ericcarmi/3WDrobot/CAD files/lens/lensconnect.stl

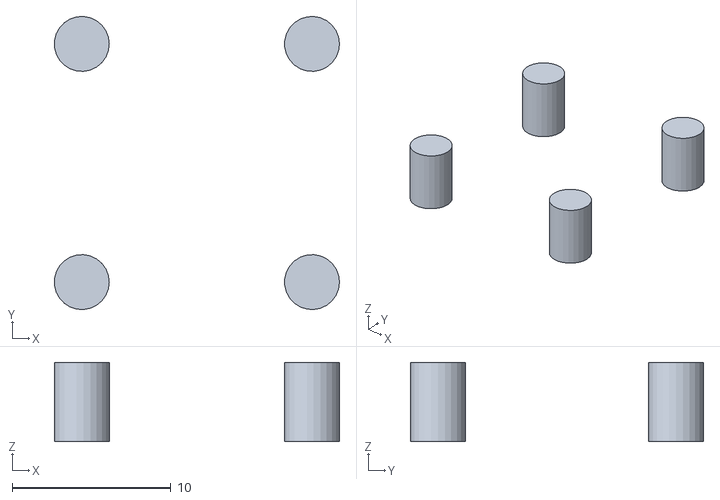
[picture p16: CAD file, 2020-05-03]
CAD files/lens/lensconnect.stl
18.0 x 18.5 x 5.00
