ericcarmi/3WDrobot/CAD files/hBridgeHolder.stl

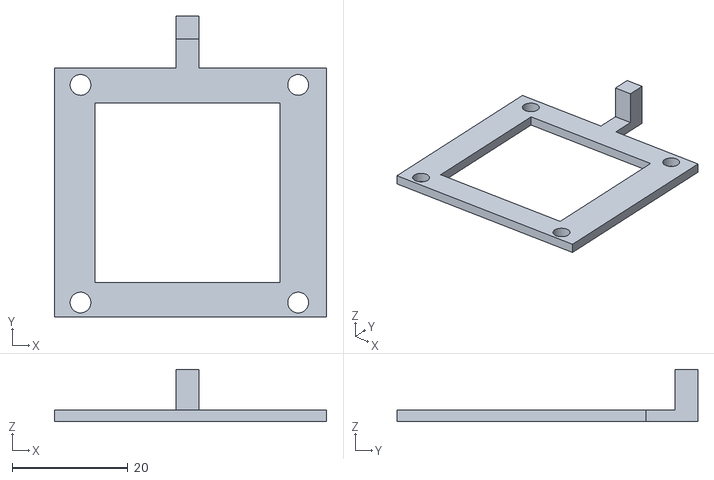
[picture p17: CAD file, 2020-05-03]
CAD files/hBridgeHolder.stl
47.0 x 52.0 x 9.00
