ericcarmi/3WDrobot/CAD files/cammountUnderBase.stl

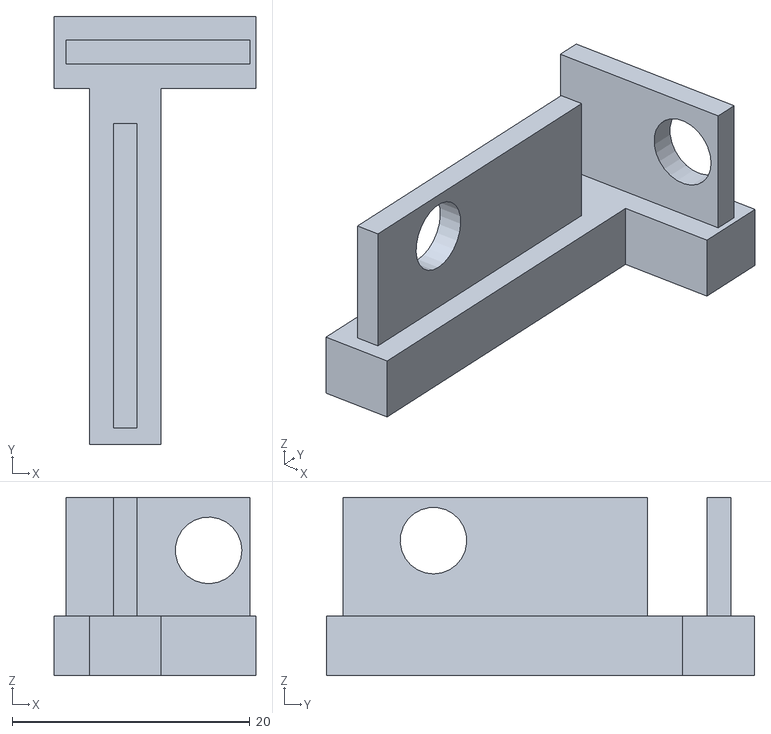
[picture p18: CAD file, 2020-05-03]
CAD files/cammountUnderBase.stl
17.0 x 36.0 x 15.0
