ericcarmi/3WDrobot/CAD files/cameraMount3.stl

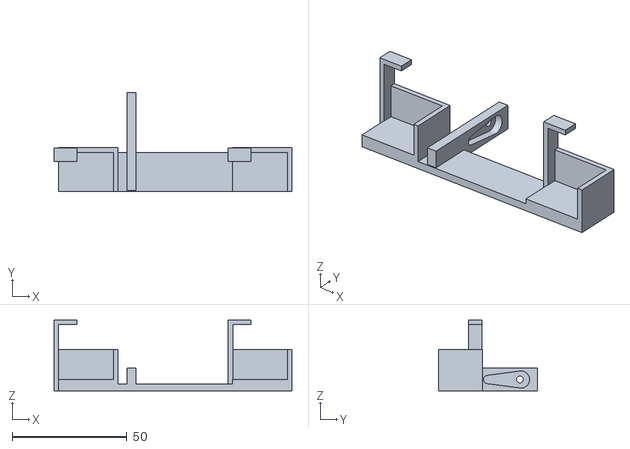
[picture p19: CAD file, 2020-05-03]
CAD files/cameraMount3.stl
103.9 x 43.0 x 31.0
