ericcarmi/3WDrobot/CAD files/robotmount.stl

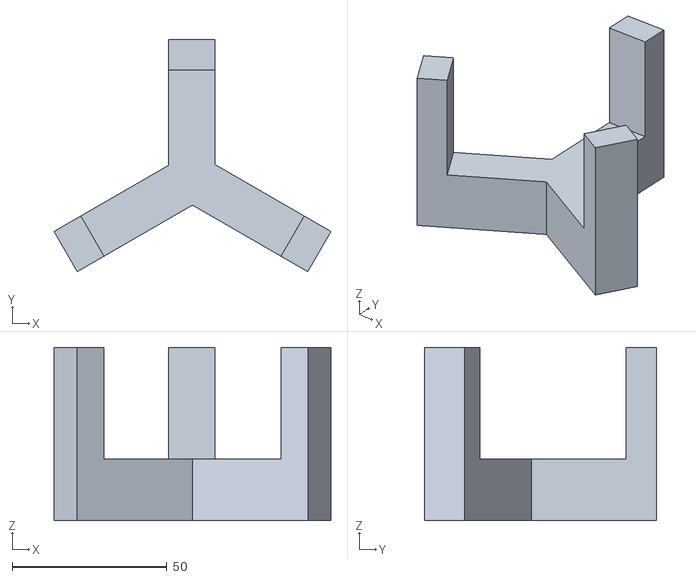
[picture p20: CAD file, 2020-05-03]
CAD files/robotmount.stl
89.5 x 75.1 x 56.0
