ericcarmi/3WDrobot/CAD files/stpprMicTop.stl

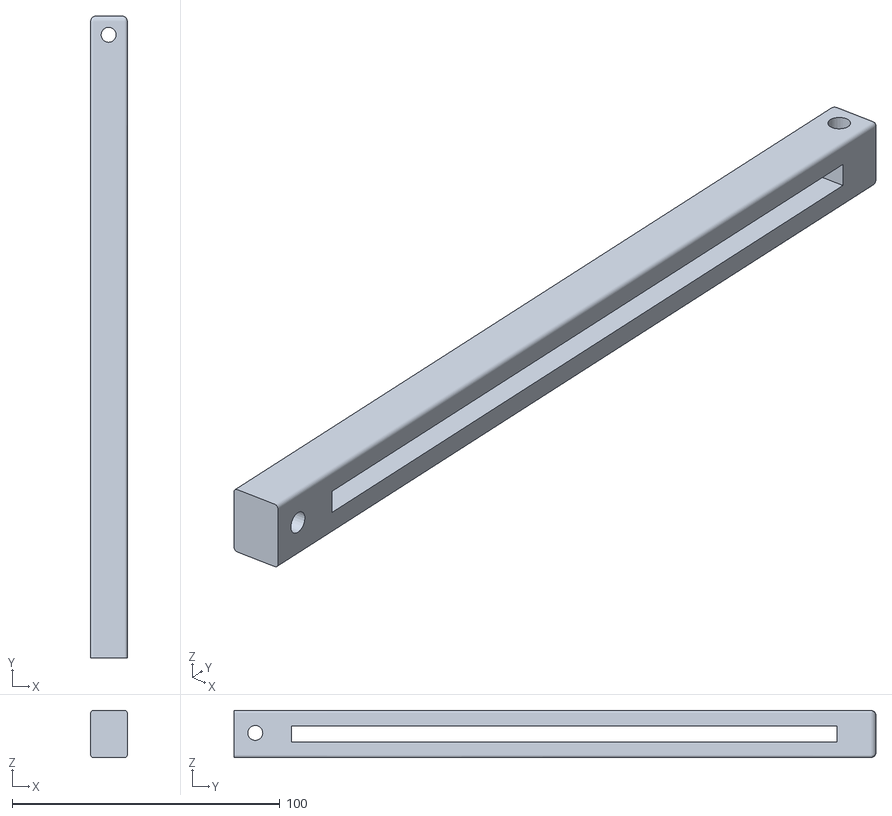
[picture p21: CAD file, 2020-05-03]
CAD files/stpprMicTop.stl
13.7 x 240.0 x 17.7
