ericcarmi/3WDrobot/CAD files/cammountBase.stl

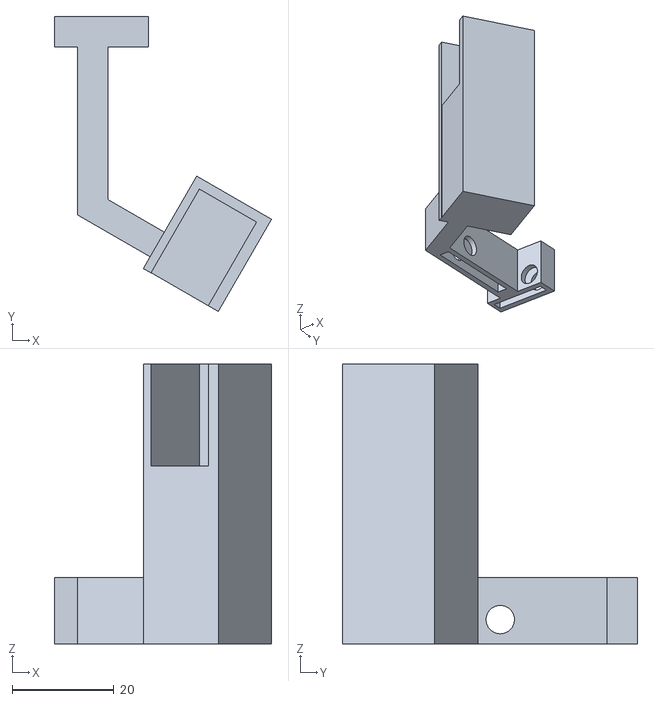
[picture p22: CAD file, 2020-05-03]
CAD files/cammountBase.stl
42.7 x 58.0 x 55.0
