ericcarmi/3WDrobot/CAD files/stpprtopbranch.stl

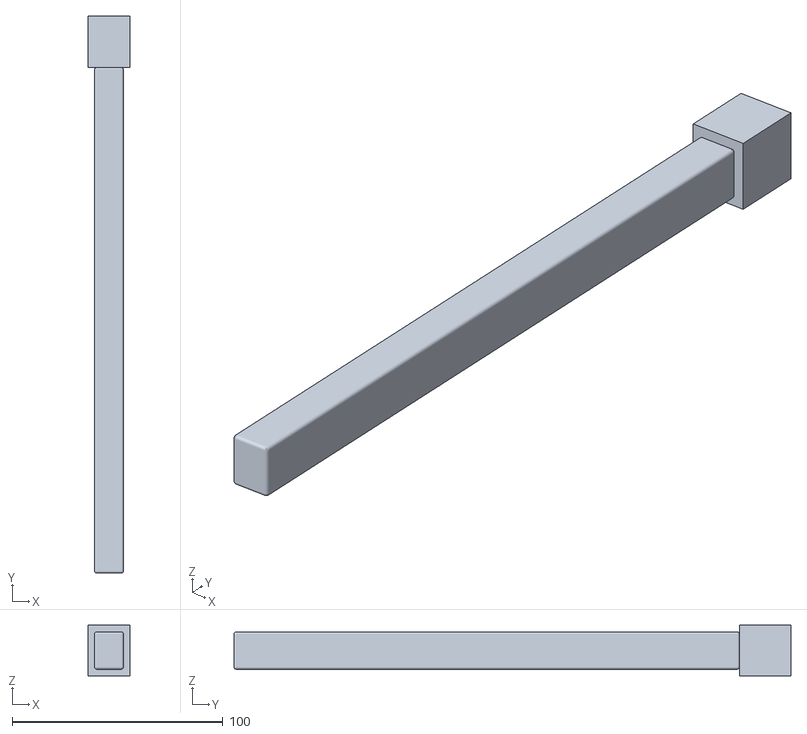
[picture p23: CAD file, 2020-05-03]
CAD files/stpprtopbranch.stl
20.0 x 264.5 x 24.0
