ericcarmi/3WDrobot/CAD files/speakercab.stl

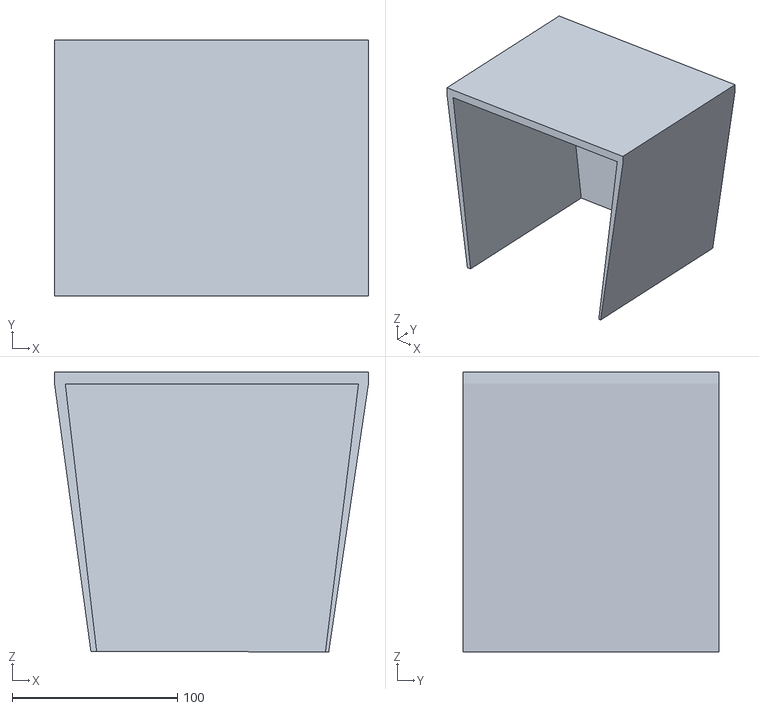
[picture p24: CAD file, 2020-05-03]
CAD files/speakercab.stl
190.0 x 155.0 x 169.3
